nasp2000/LPT-UNO/images/image4.png

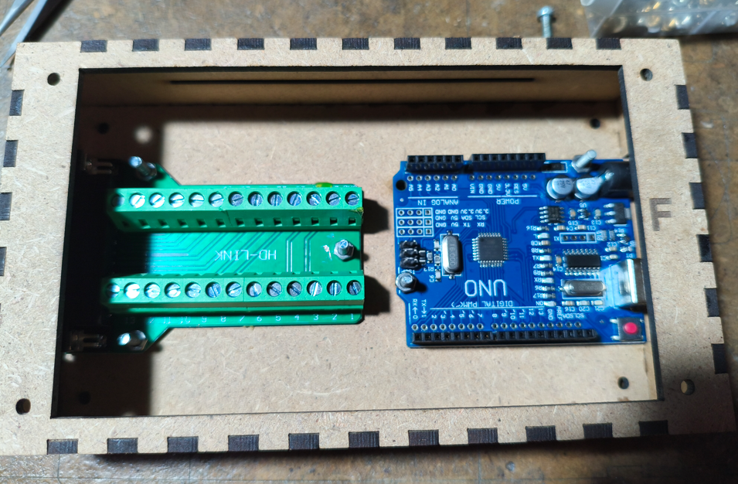
images/image4.png
